Dudmahn/LapRSSI/test/test_data/2017-09-29/IMAG0639.jpg

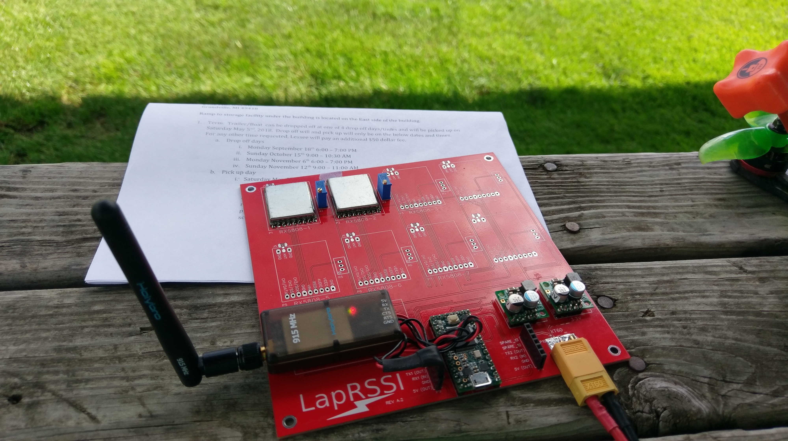
test/test_data/2017-09-29/IMAG0639.jpg
