Dudmahn/LapRSSI/test/test_data/2017-10-10/race_2.png

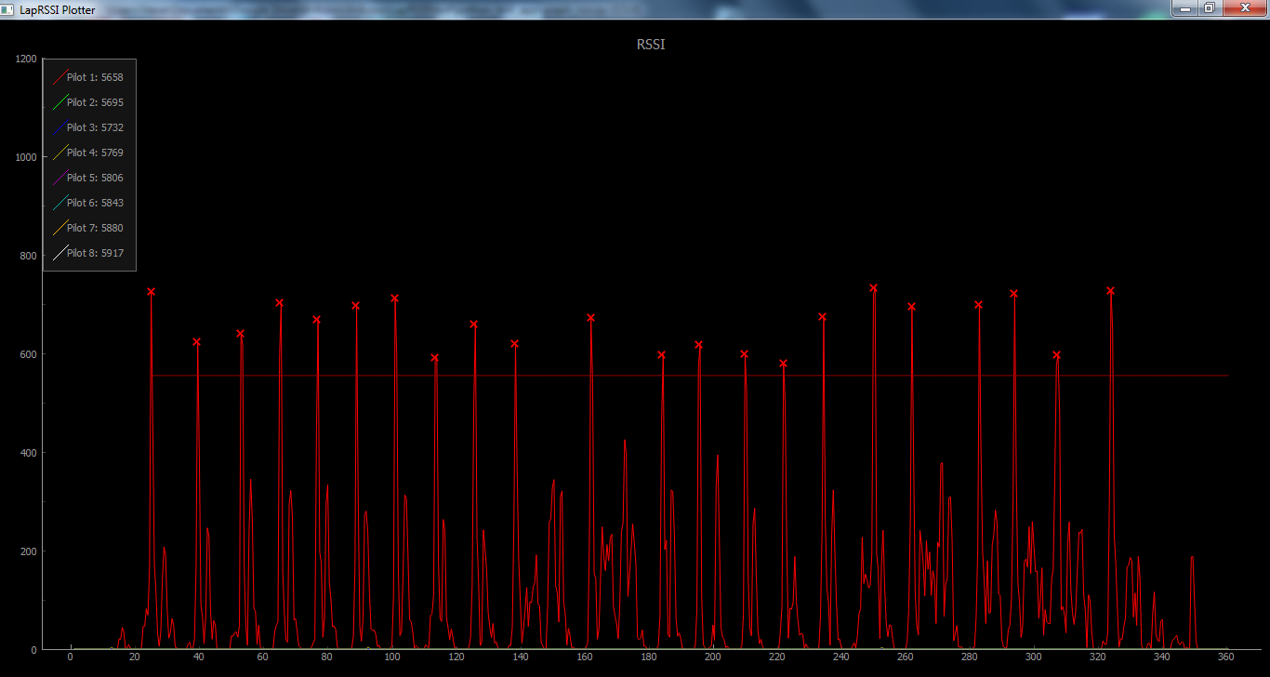
test/test_data/2017-10-10/race_2.png
