Dudmahn/LapRSSI/test/test_data/2017-10-10/race_5.png

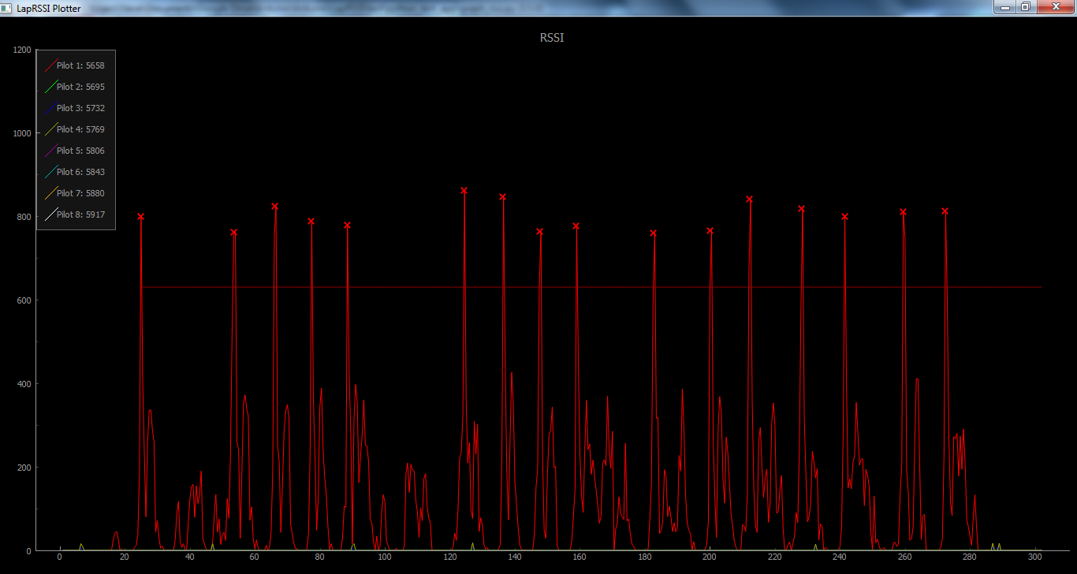
test/test_data/2017-10-10/race_5.png
